kushnirova/FireWheels/photos/pcb_2.jpg

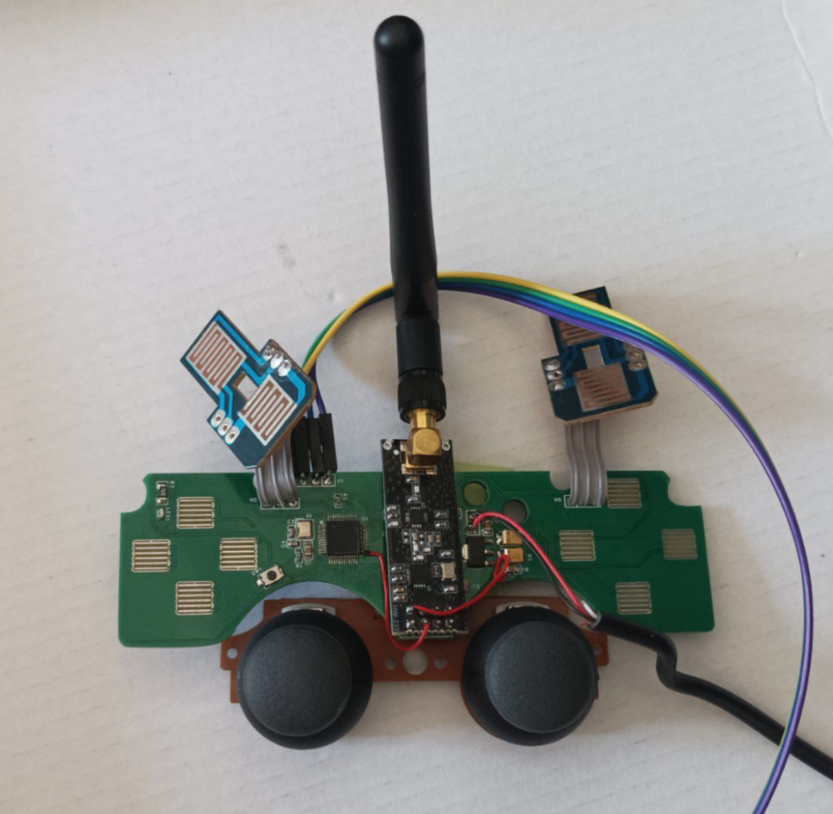
photos/pcb_2.jpg
