kushnirova/FireWheels/3d_models/Final3D_overview_1C.png

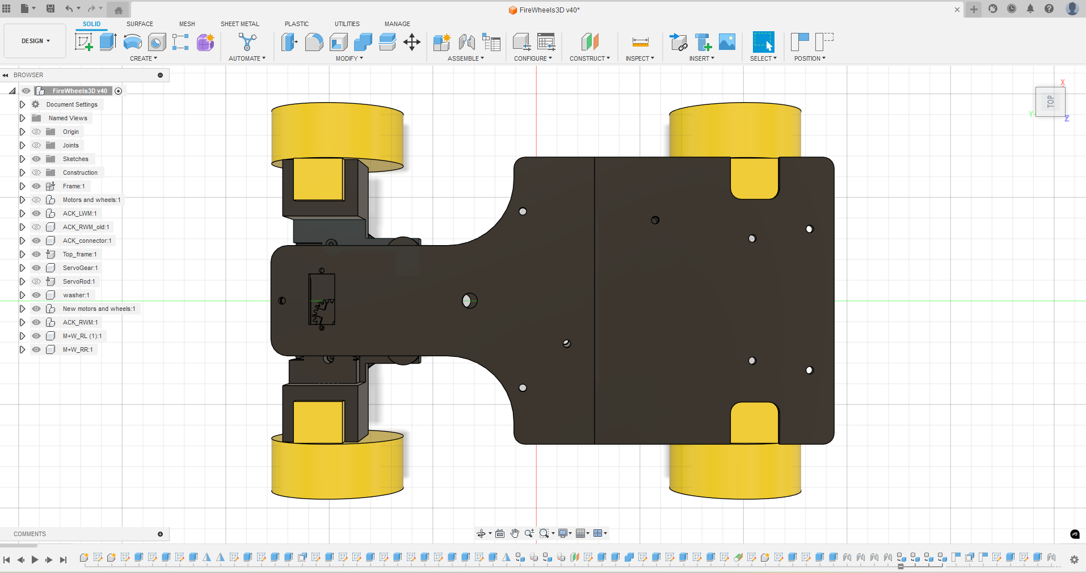
3d_models/Final3D_overview_1C.png
