kushnirova/FireWheels/3d_models/WIP_overview_1D.png

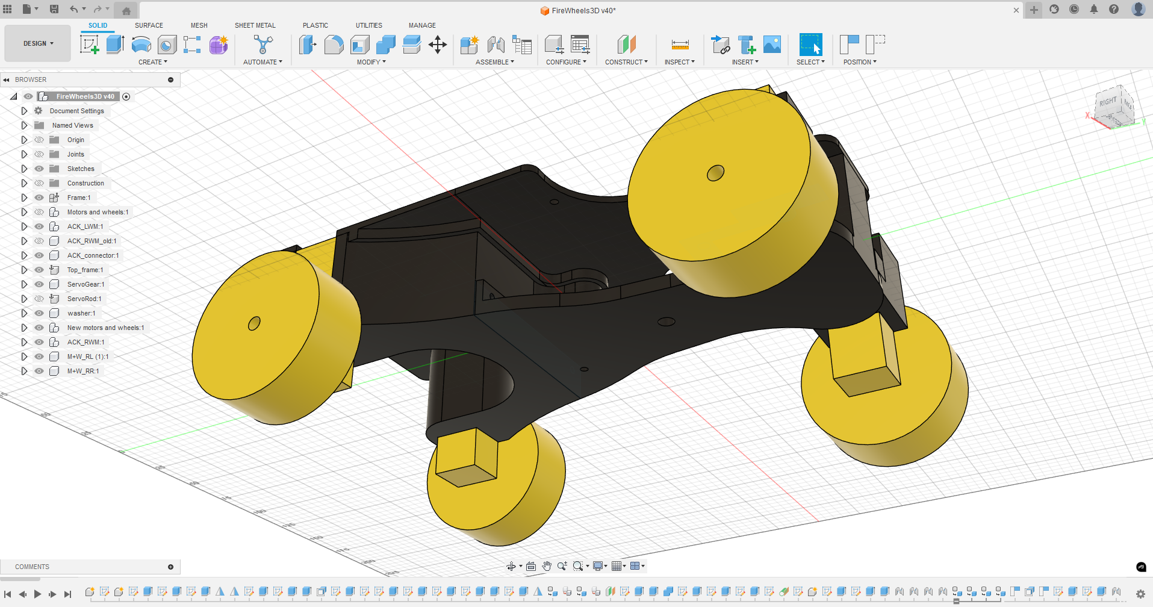
3d_models/WIP_overview_1D.png
