kushnirova/FireWheels/FireWheelsApp/images/awaryjne.jpg

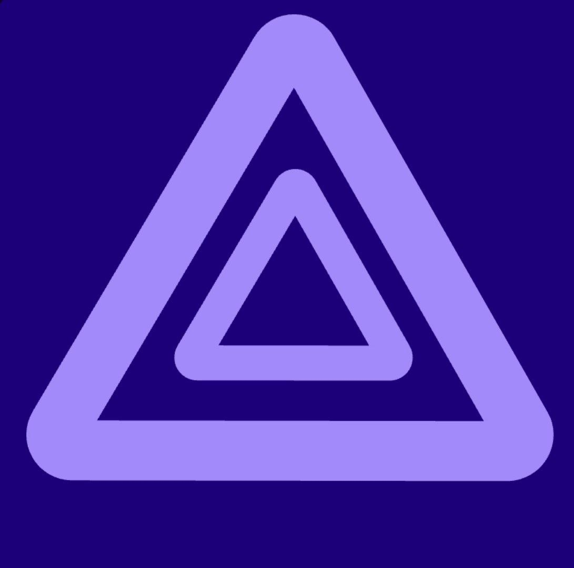
FireWheelsApp/images/awaryjne.jpg
