kushnirova/FireWheels/FireWheelsApp/images/awaryjne_on.jpg

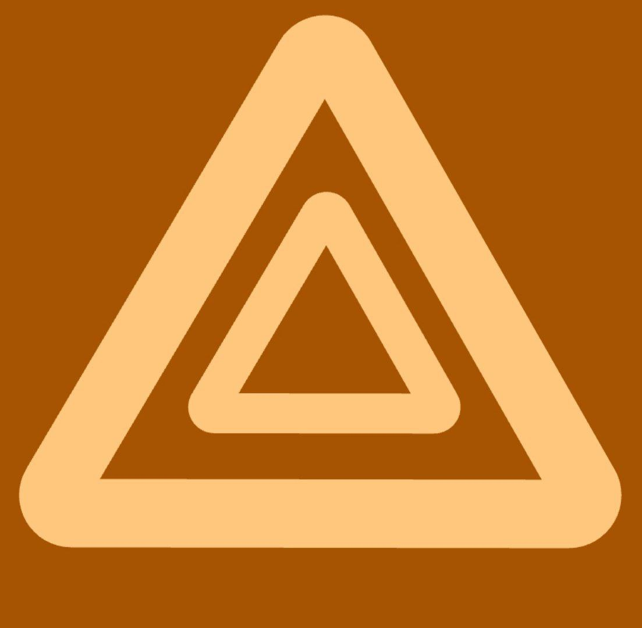
FireWheelsApp/images/awaryjne_on.jpg
