kushnirova/FireWheels/FireWheelsApp/images/drift.jpg

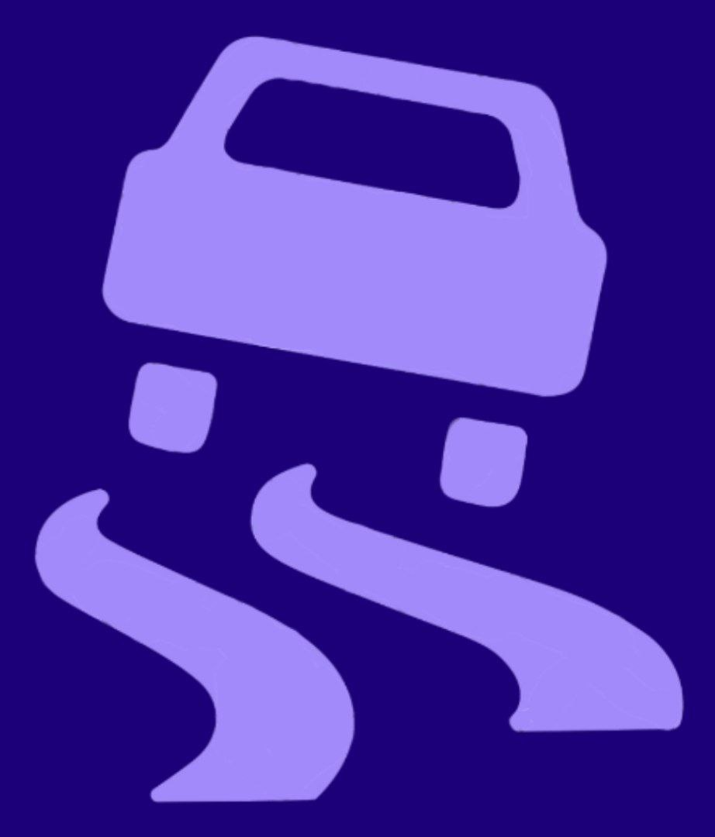
FireWheelsApp/images/drift.jpg
