kushnirova/FireWheels/FireWheelsApp/images/klakson.jpg

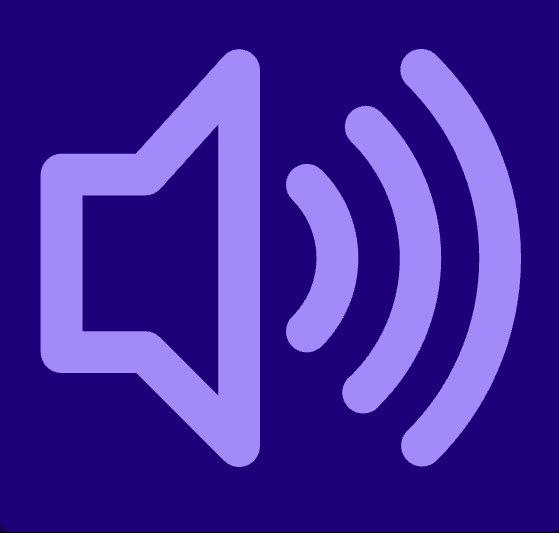
FireWheelsApp/images/klakson.jpg
