kushnirova/FireWheels/FireWheelsApp/images/lewo.jpg

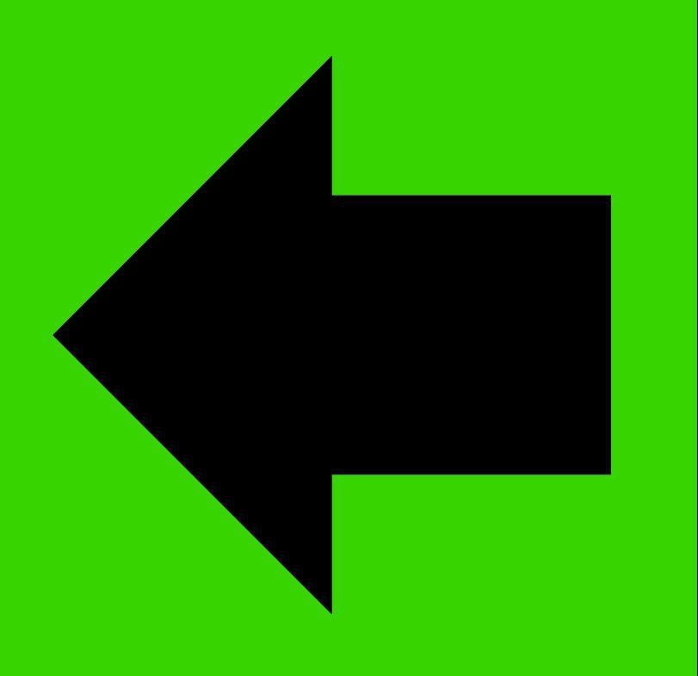
FireWheelsApp/images/lewo.jpg
