kushnirova/FireWheels/FireWheelsApp/images/minus.jpg

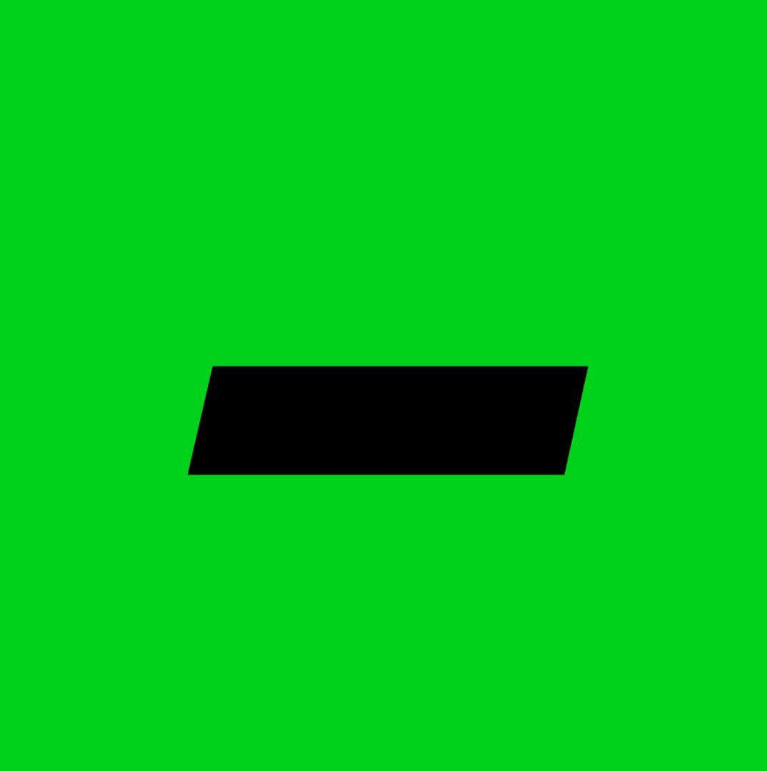
FireWheelsApp/images/minus.jpg
