kushnirova/FireWheels/FireWheelsApp/images/plus.jpg

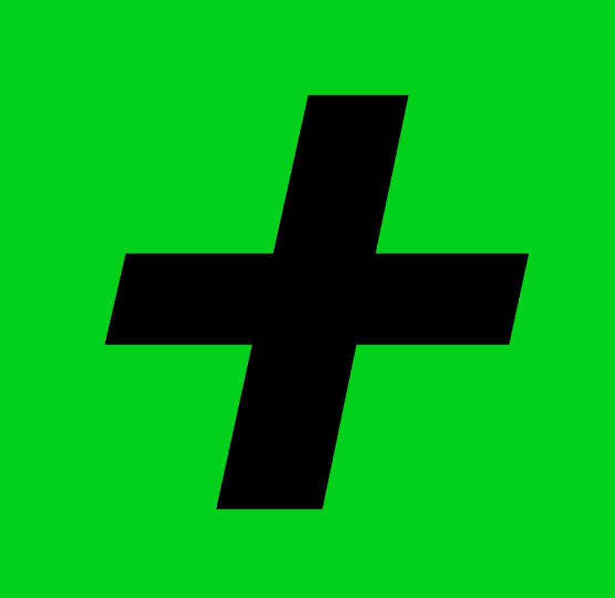
FireWheelsApp/images/plus.jpg
