kushnirova/FireWheels/FireWheelsApp/images/prawo.jpg

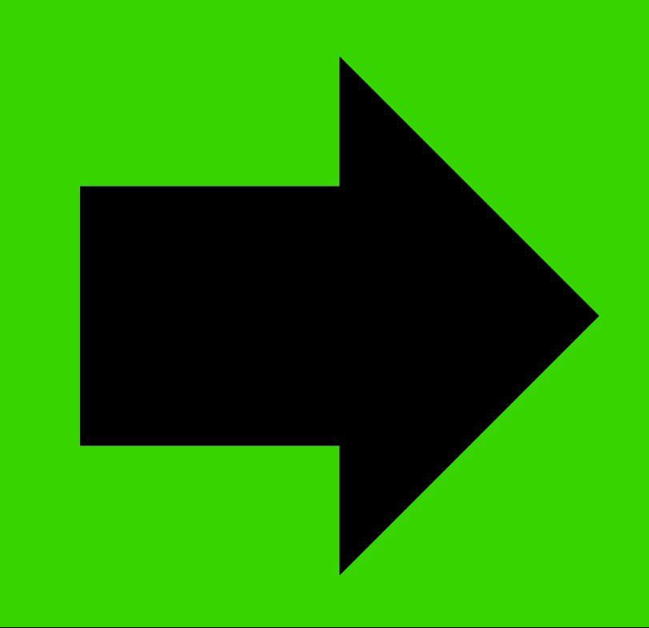
FireWheelsApp/images/prawo.jpg
