kushnirova/FireWheels/FireWheelsApp/images/przod.jpg

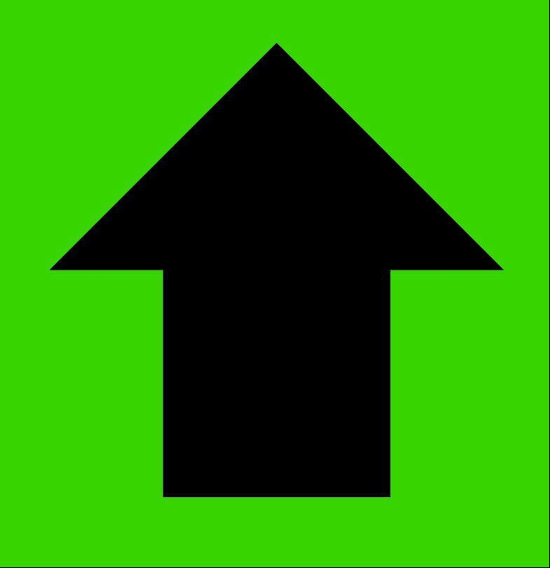
FireWheelsApp/images/przod.jpg
