kushnirova/FireWheels/FireWheelsApp/images/stop.jpg

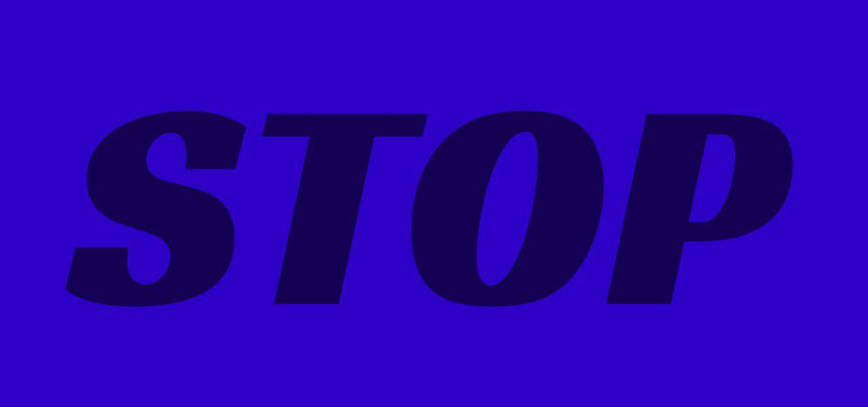
FireWheelsApp/images/stop.jpg
