kushnirova/FireWheels/FireWheelsApp/images/swiatla.jpg

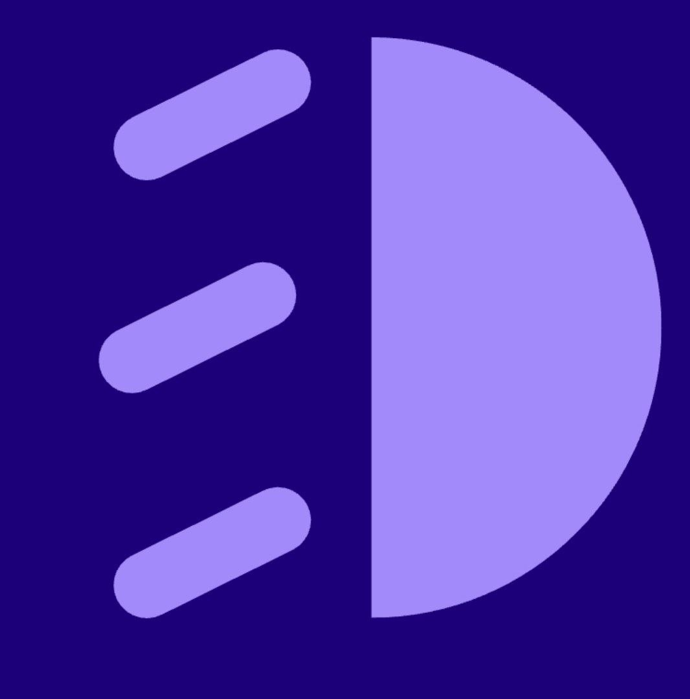
FireWheelsApp/images/swiatla.jpg
