kushnirova/FireWheels/FireWheelsApp/images/tryb.jpg

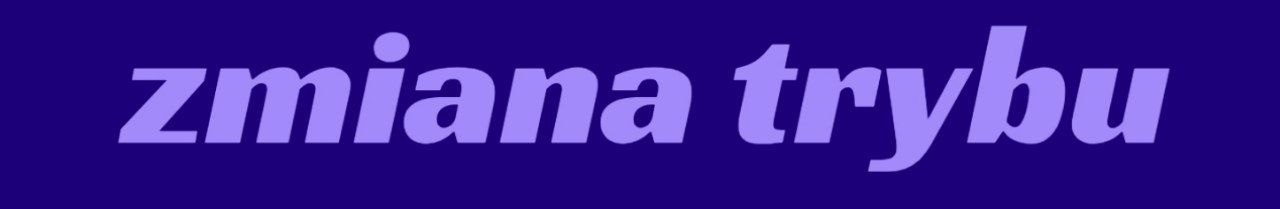
FireWheelsApp/images/tryb.jpg
