kushnirova/FireWheels/FireWheelsApp/images/tyl.jpg

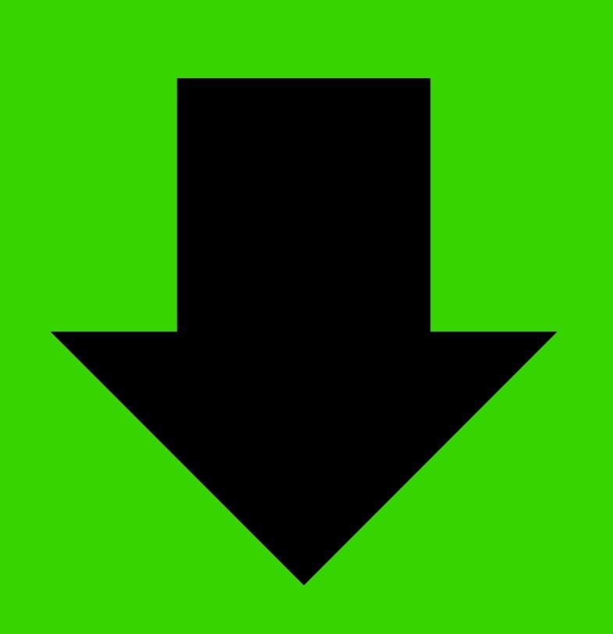
FireWheelsApp/images/tyl.jpg
