kushnirova/FireWheels/photos/front.jpg

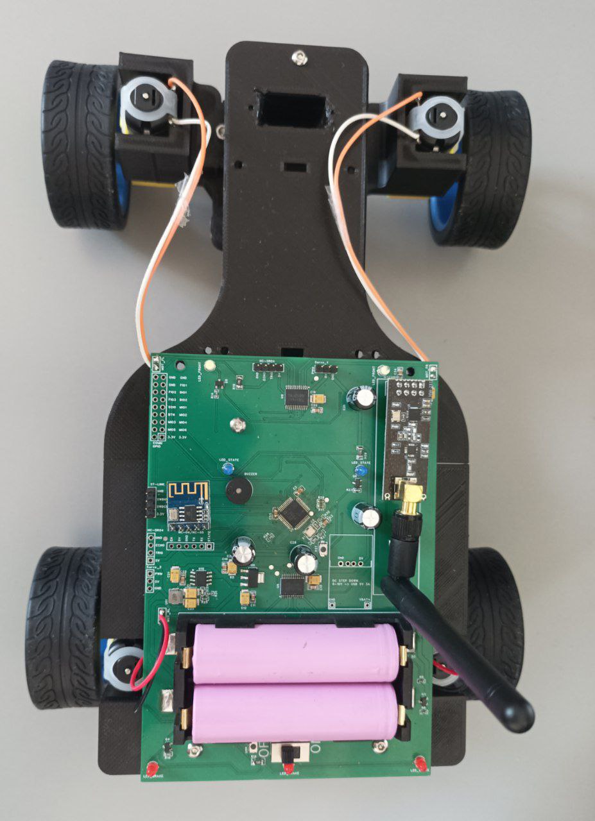
photos/front.jpg
