kushnirova/FireWheels/photos/front_left.jpg

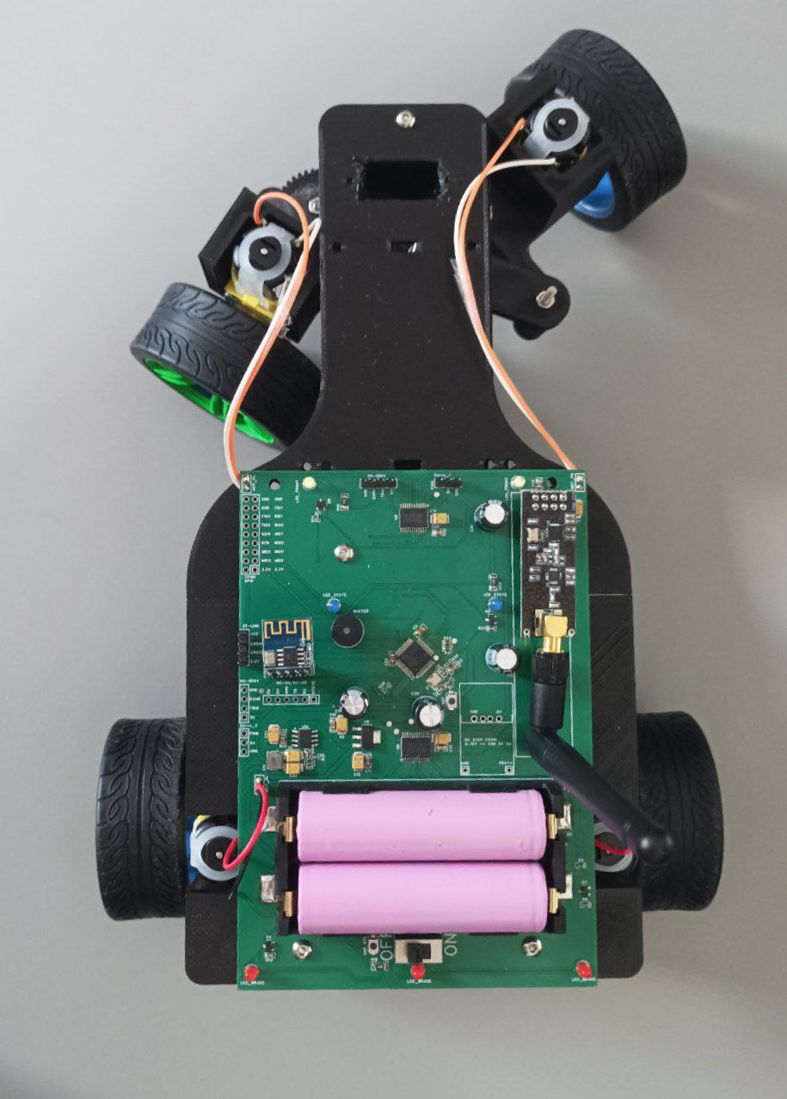
photos/front_left.jpg
