kushnirova/FireWheels/photos/front_right.jpg

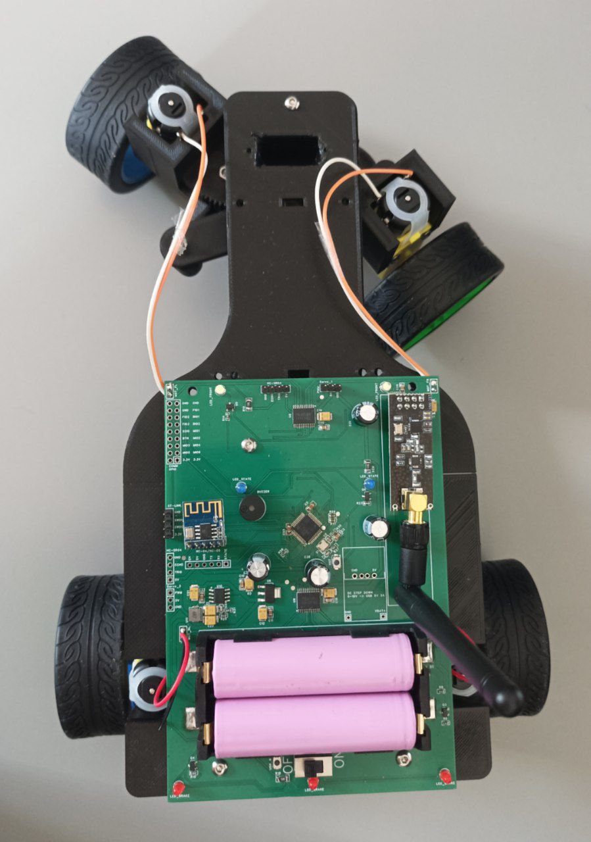
photos/front_right.jpg
