kushnirova/FireWheels/photos/pcb_1.jpg

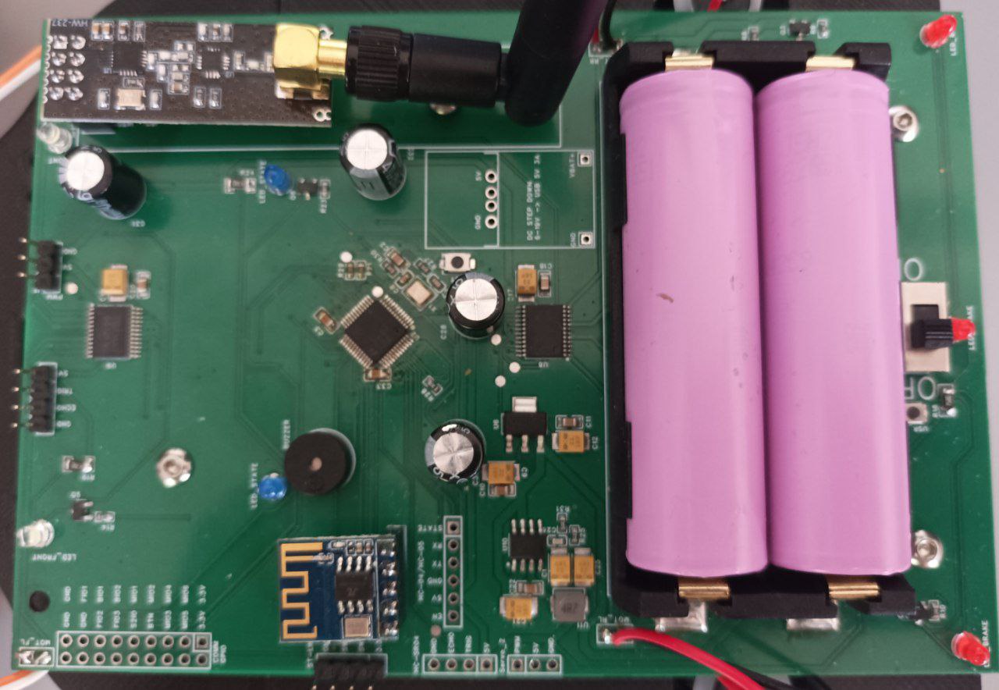
photos/pcb_1.jpg
