kushnirova/FireWheels/photos/side.jpg

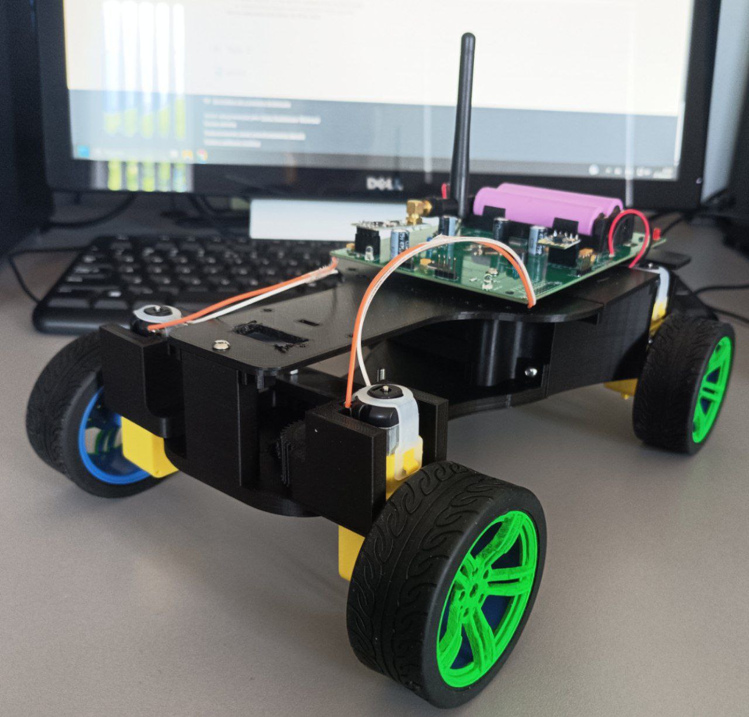
photos/side.jpg
