kushnirova/FireWheels/schematic_pcb/PDF_PNG/PCB_MOTHERBOARD_SIDE_B.png

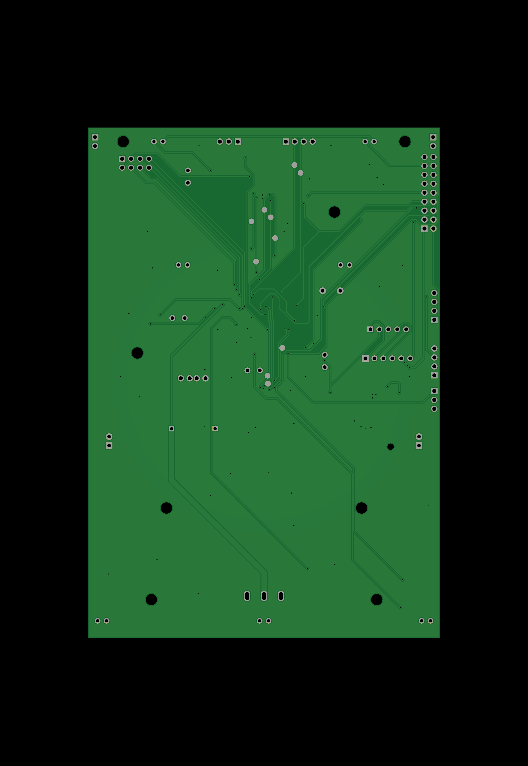
schematic_pcb/PDF_PNG/PCB_MOTHERBOARD_SIDE_B.png
