kushnirova/FireWheels/schematic_pcb/PDF_PNG/PCB_RC_PAD_SIDE_A.png

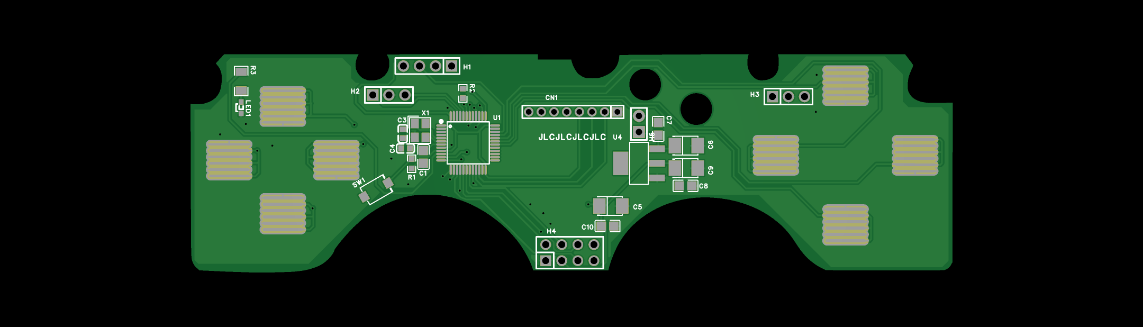
schematic_pcb/PDF_PNG/PCB_RC_PAD_SIDE_A.png
