kushnirova/FireWheels/3d_models/STLs/v2/ACK_LWM_Combined.stl

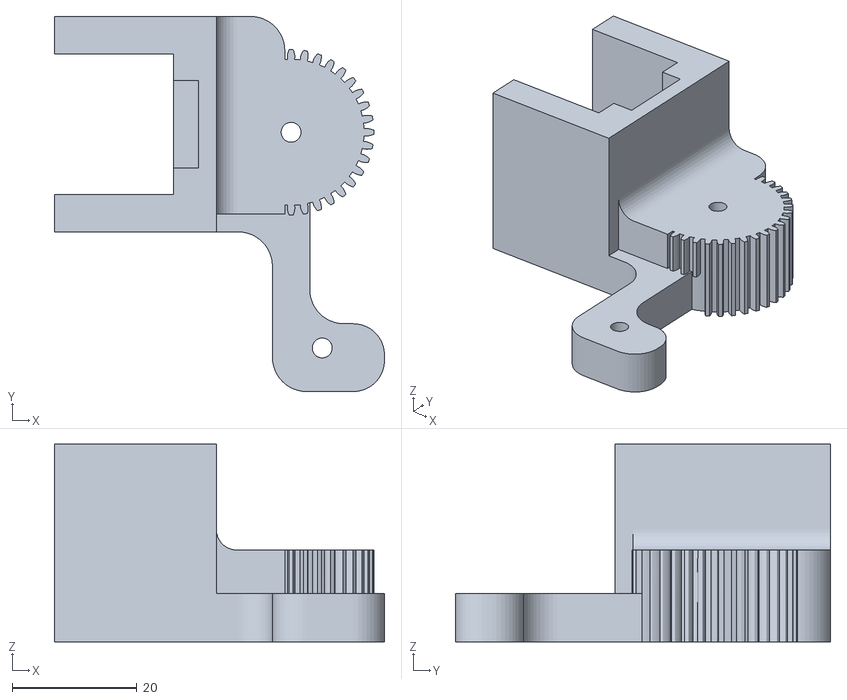
[picture p45: CAD file, 2025-06-03, an earlier design]
3d_models/STLs/v2/ACK_LWM_Combined.stl
53.0 x 60.2 x 31.7
