kushnirova/FireWheels/3d_models/STLs/v1/ACK_RWM.stl

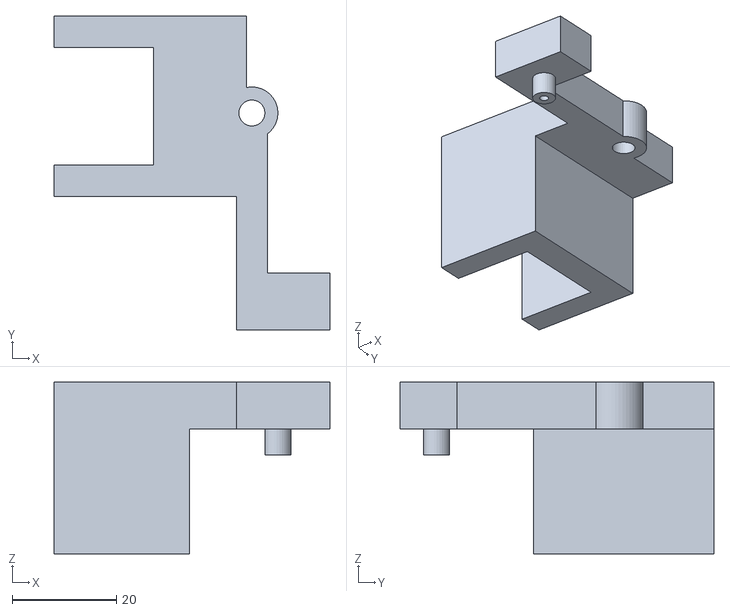
[picture p46: CAD file, 2025-05-19, an earlier design]
3d_models/STLs/v1/ACK_RWM.stl
53.0 x 60.2 x 33.0
